shm-dmitry/pantry_signal_system/3d_models/flooding-sensor.FCStd

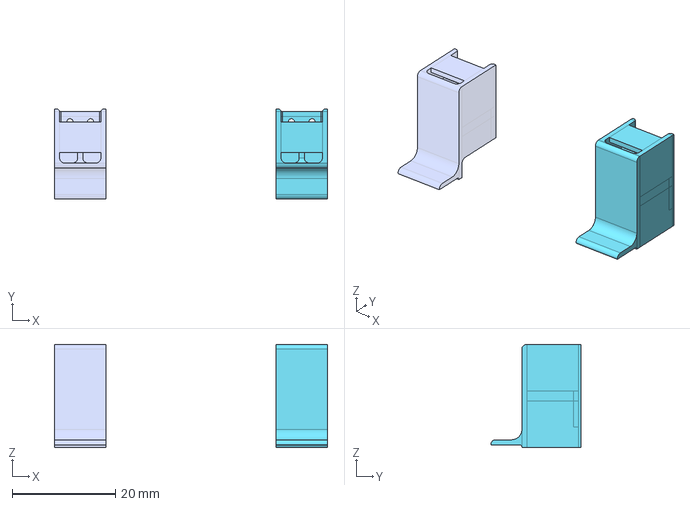
[picture p15: CAD file, 2022-12-06]
3d_models/flooding-sensor.FCStd
53.0 x 17.5 x 20.0 mm
right-side
left-side
