shm-dmitry/pantry_signal_system/3d_models/pantry_box-cup.stl

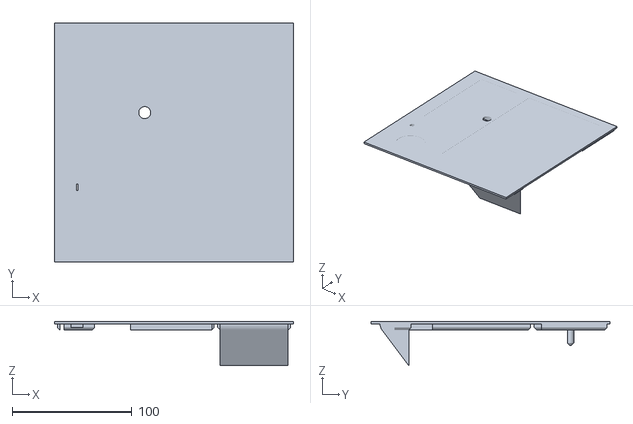
[picture p16: CAD file, 2022-12-06]
3d_models/pantry_box-cup.stl
200.0 x 200.0 x 37.0
