shm-dmitry/pantry_signal_system/3d_models/internal-flooding-sensor.FCStd

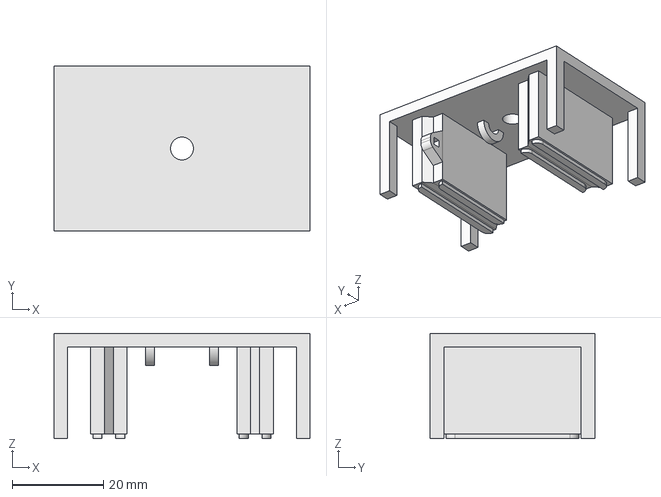
[picture p17: CAD file, 2022-07-20]
3d_models/internal-flooding-sensor.FCStd
56.0 x 36.0 x 23.0 mm
