shm-dmitry/pantry_signal_system/3d_models/supply-module-box-box.stl

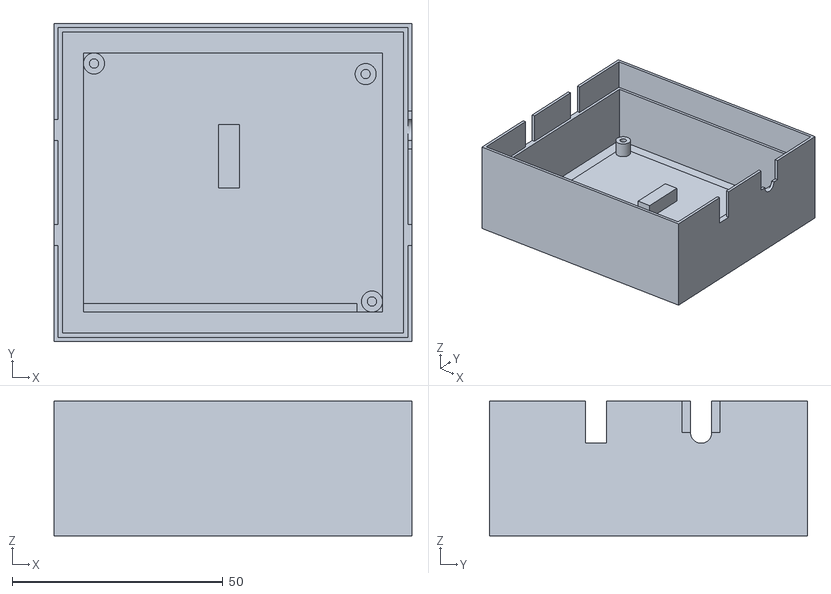
[picture p18: CAD file, 2022-04-04]
3d_models/supply-module-box-box.stl
85.0 x 75.5 x 32.0
