shm-dmitry/pantry_signal_system/3d_models/control-module-box-front.stl

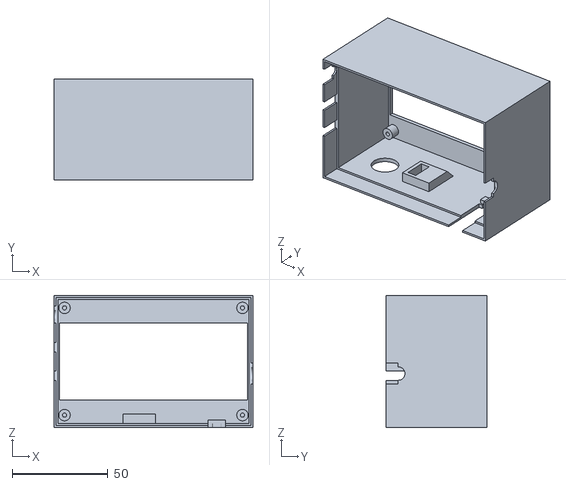
[picture p19: CAD file, 2022-04-04]
3d_models/control-module-box-front.stl
104.0 x 53.0 x 69.0
