shm-dmitry/pantry_signal_system/3d_models/23a-battery-container-box.stl

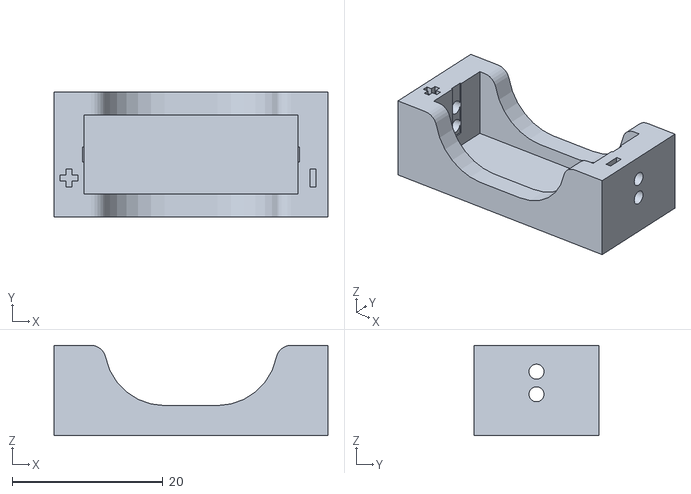
[picture p20: CAD file, 2022-04-04]
3d_models/23a-battery-container-box.stl
36.4 x 16.6 x 12.0
