shm-dmitry/pantry_signal_system/3d_models/23a-battery-container.FCStd

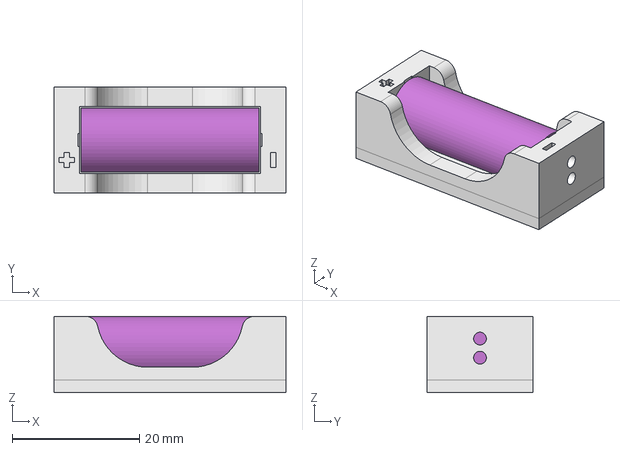
[picture p21: CAD file, 2022-04-04]
3d_models/23a-battery-container.FCStd
36.4 x 16.6 x 12.0 mm
battery-dont-print
