shm-dmitry/pantry_signal_system/3d_models/supply-module-box-cup.stl

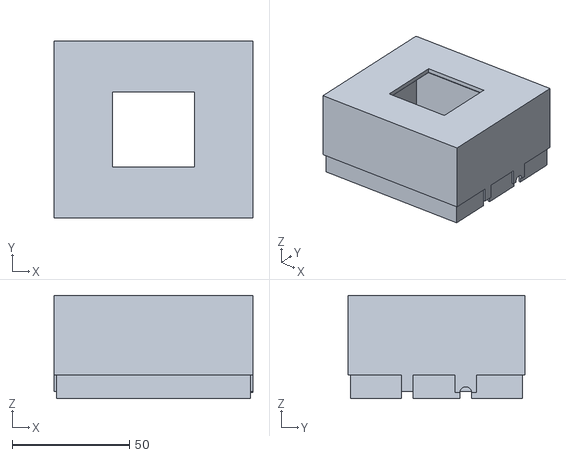
[picture p22: CAD file, 2022-04-04]
3d_models/supply-module-box-cup.stl
85.0 x 75.5 x 44.0
