shm-dmitry/pantry_signal_system/3d_models/control-module-box.FCStd

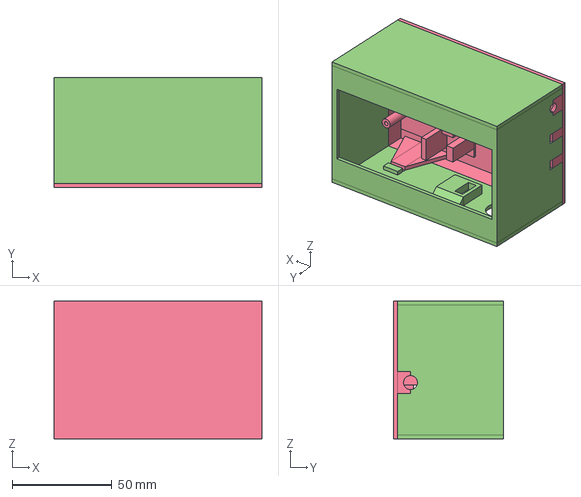
[picture p23: CAD file, 2022-04-04]
3d_models/control-module-box.FCStd
104.0 x 55.0 x 69.0 mm
front
back
