shm-dmitry/pantry_signal_system/3d_models/supply-module-box.FCStd

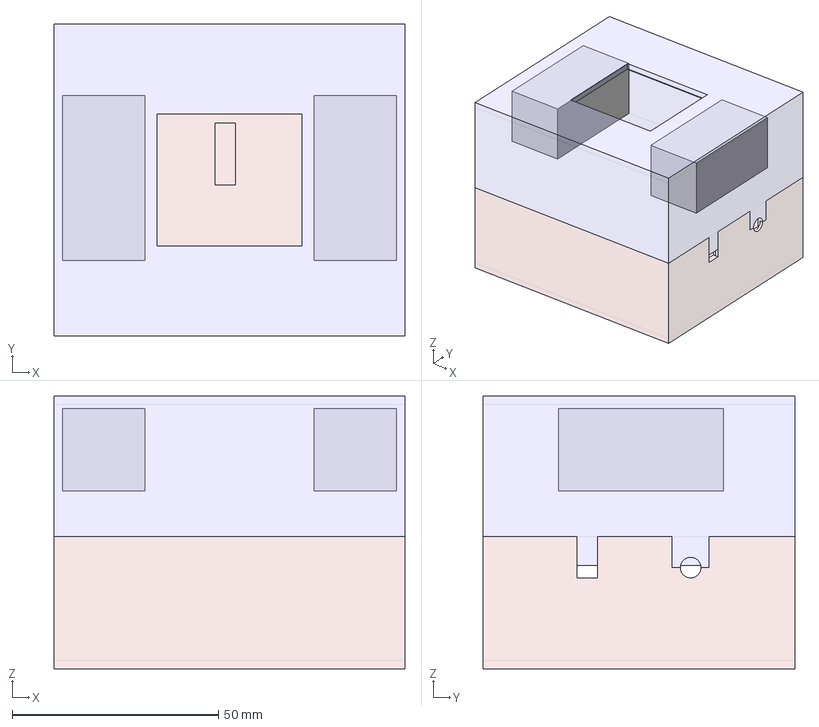
[picture p24: CAD file, 2022-04-04]
3d_models/supply-module-box.FCStd
85.0 x 75.5 x 66.0 mm
cup
alcaline-emulator-dont-print
