shm-dmitry/pantry_signal_system/3d_models/control-module-box-back.stl

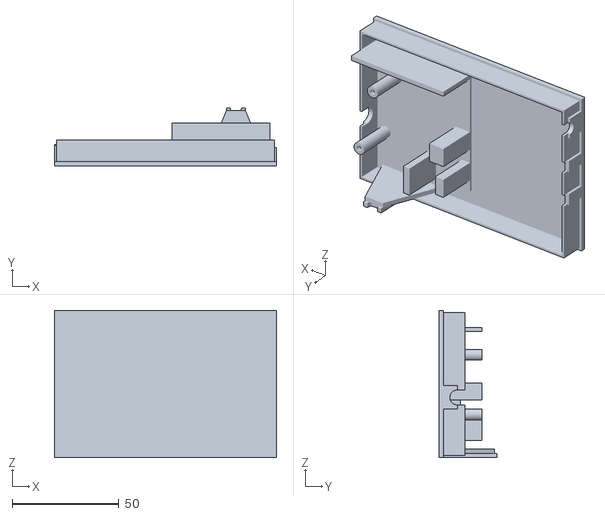
[picture p25: CAD file, 2022-03-22]
3d_models/control-module-box-back.stl
104.0 x 27.0 x 69.0
