shm-dmitry/pantry_signal_system/3d_models/air-fan-income.FCStd

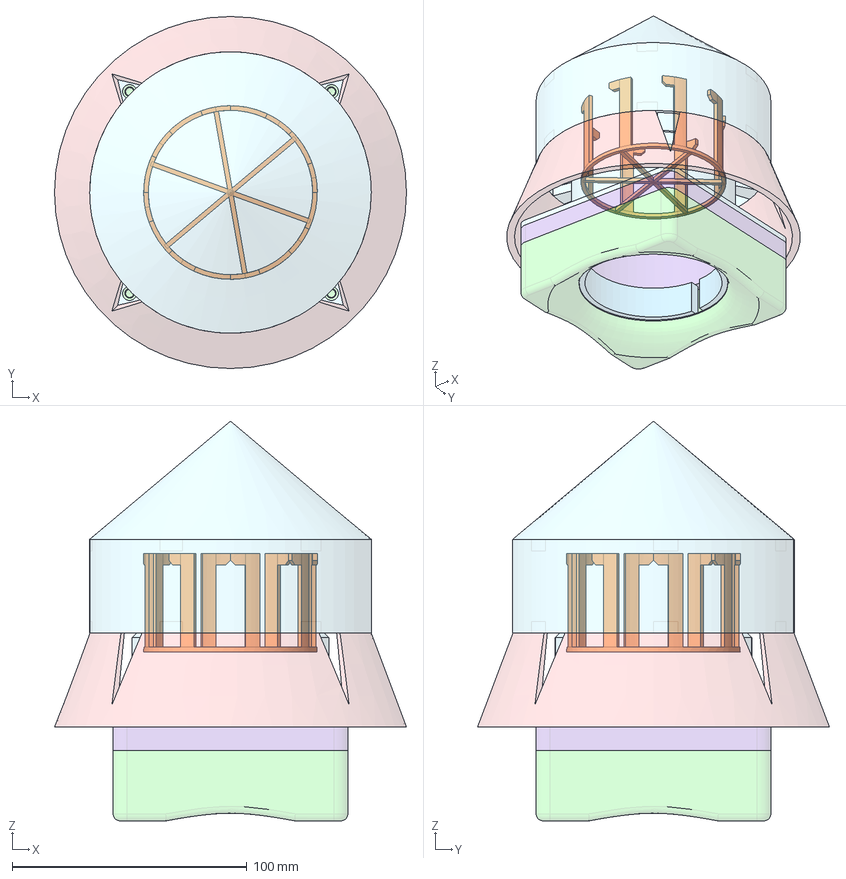
[picture p26: CAD file, 2022-03-19]
3d_models/air-fan-income.FCStd
150.0 x 150.0 x 170.3 mm
plate
top
filter
support
cap
cup-support
