shm-dmitry/pantry_signal_system/3d_models/air-fan-outcome.FCStd

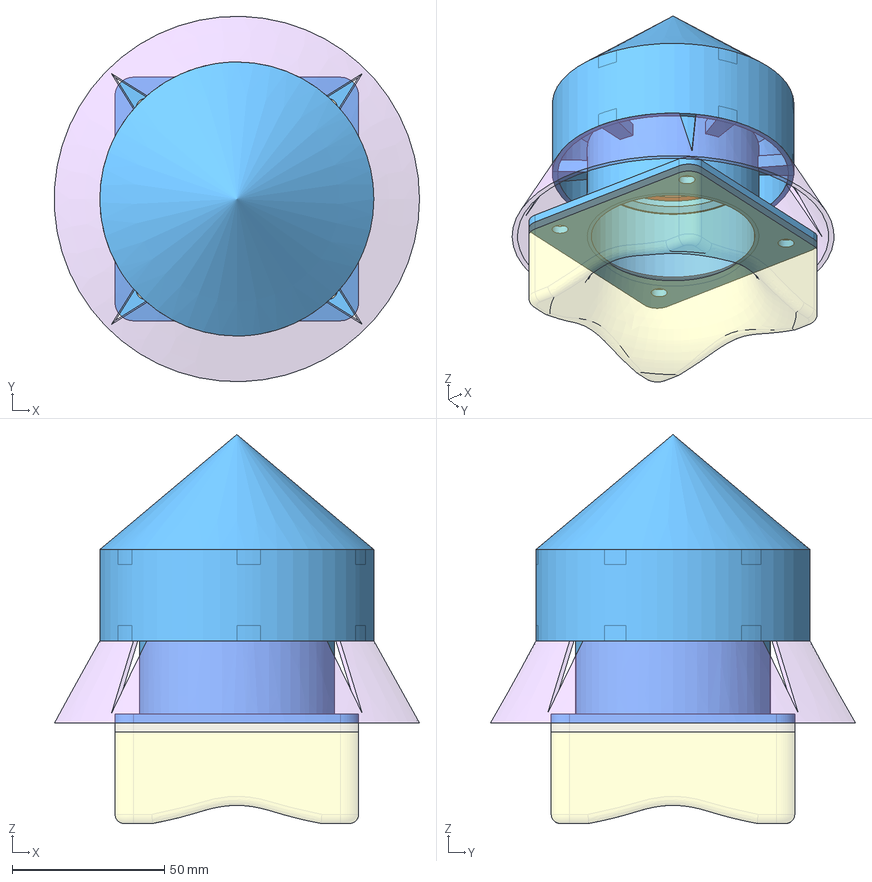
[picture p27: CAD file, 2022-03-19]
3d_models/air-fan-outcome.FCStd
119.9 x 119.9 x 127.8 mm
plate
top
filter
support
cup
