shm-dmitry/pantry_signal_system/3d_models/air-fan-box.FCStd

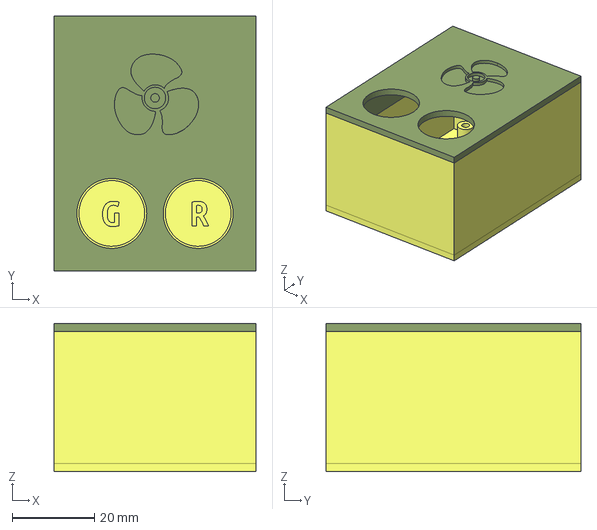
[picture p28: CAD file, 2022-03-19]
3d_models/air-fan-box.FCStd
49.0 x 62.0 x 36.0 mm
top
