shm-dmitry/pantry_signal_system/3d_models/air-fan-income-cap-support.stl

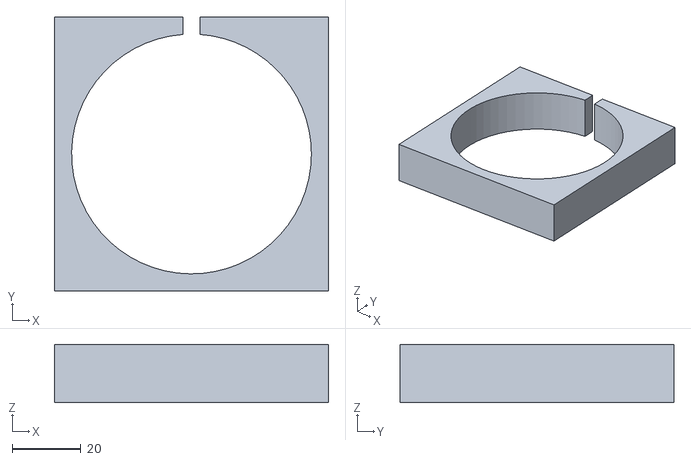
[picture p29: CAD file, 2022-03-19]
3d_models/air-fan-income-cap-support.stl
80.0 x 80.0 x 17.0
