shm-dmitry/pantry_signal_system/3d_models/air-fan-income-cap.stl

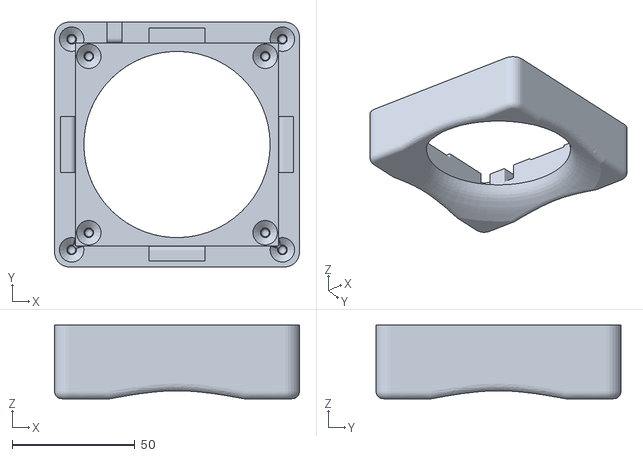
[picture p30: CAD file, 2022-03-19]
3d_models/air-fan-income-cap.stl
100.0 x 100.0 x 30.0
