shm-dmitry/pantry_signal_system/3d_models/air-fan-box-box.stl

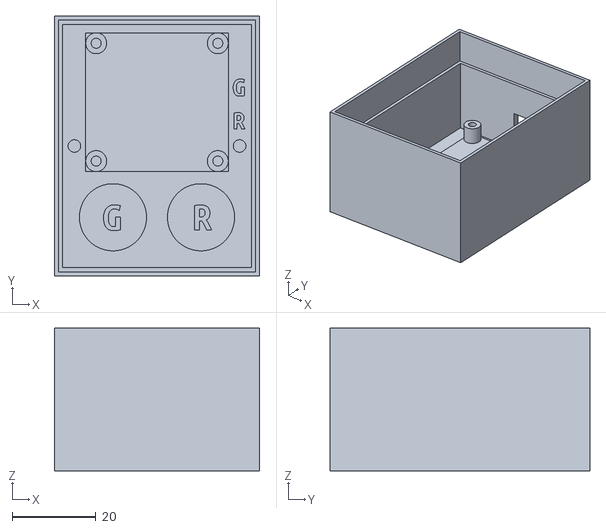
[picture p31: CAD file, 2022-03-19]
3d_models/air-fan-box-box.stl
49.0 x 62.0 x 34.0
