shm-dmitry/pantry_signal_system/3d_models/air-fan-outcome-cup.stl

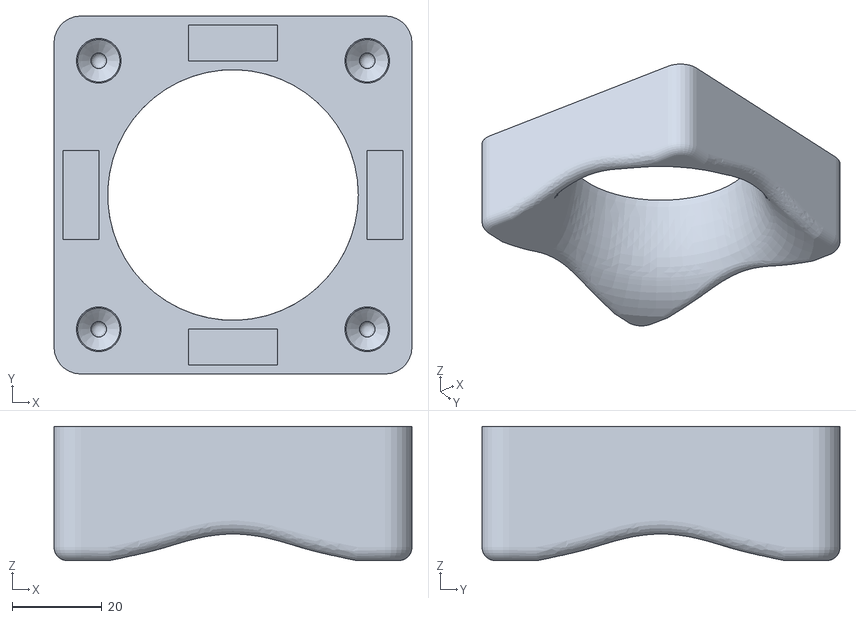
[picture p32: CAD file, 2022-03-19]
3d_models/air-fan-outcome-cup.stl
80.0 x 80.0 x 30.0
