shm-dmitry/pantry_signal_system/3d_models/air-fan-box-top.stl

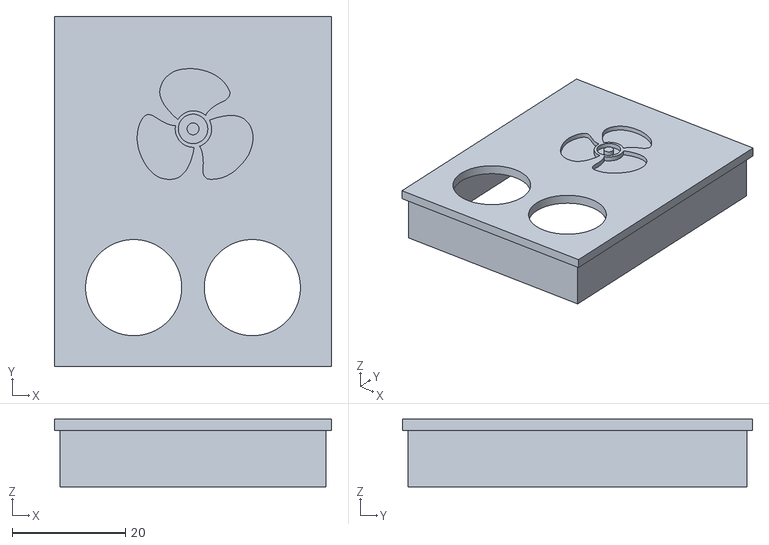
[picture p33: CAD file, 2022-03-19]
3d_models/air-fan-box-top.stl
49.0 x 62.0 x 12.0
