shm-dmitry/pantry_signal_system/3d_models/air-dryer-cup.stl

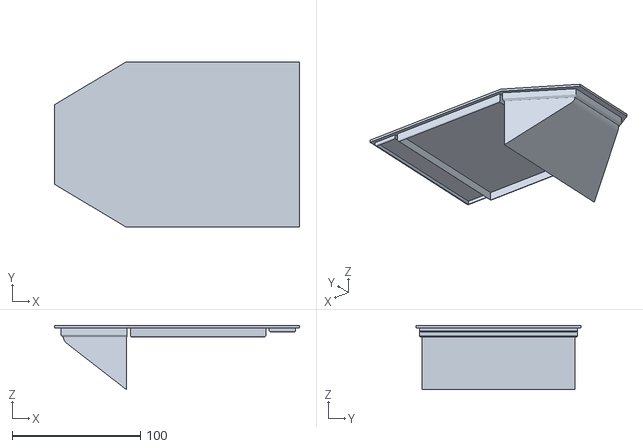
[picture p34: CAD file, 2022-03-03]
3d_models/air-dryer-cup.stl
191.0 x 129.0 x 50.0
