shm-dmitry/pantry_signal_system/3d_models/air-dryer.FCStd

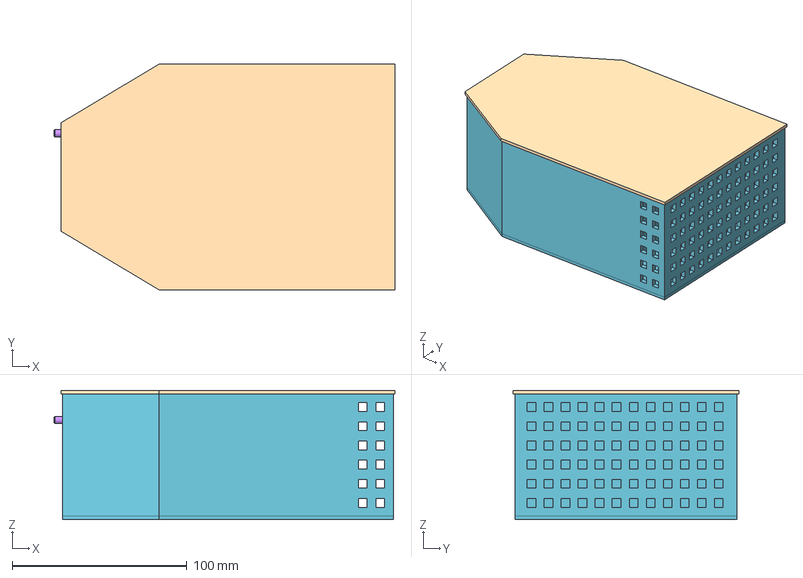
[picture p35: CAD file, 2022-03-03]
3d_models/air-dryer.FCStd
195.0 x 129.0 x 74.0 mm
container
container-cup
pin
cup
