shm-dmitry/pantry_signal_system/3d_models/air-fan-outcome-top.stl

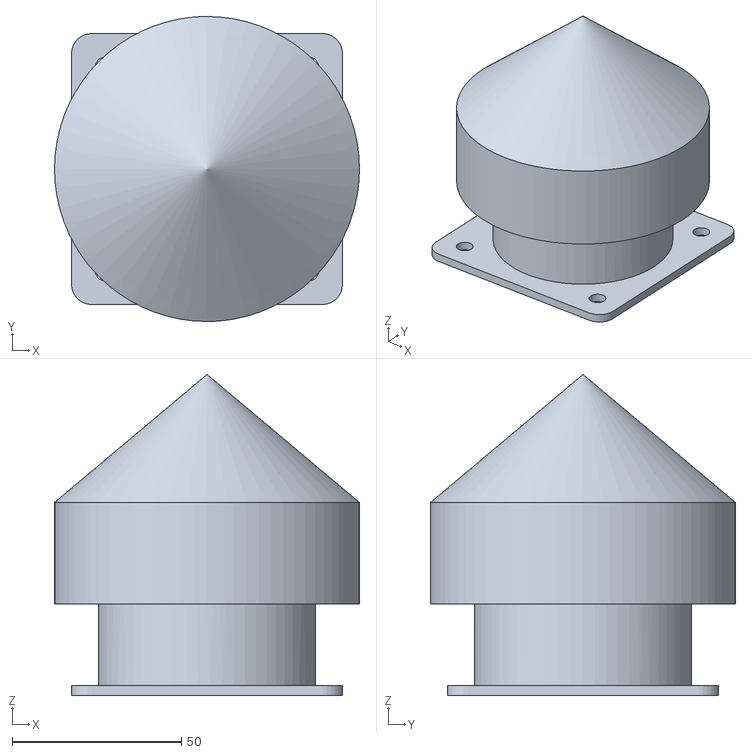
[picture p36: CAD file, 2022-03-03]
3d_models/air-fan-outcome-top.stl
90.0 x 90.0 x 94.8
