shm-dmitry/pantry_signal_system/3d_models/air-fan-income-top.stl

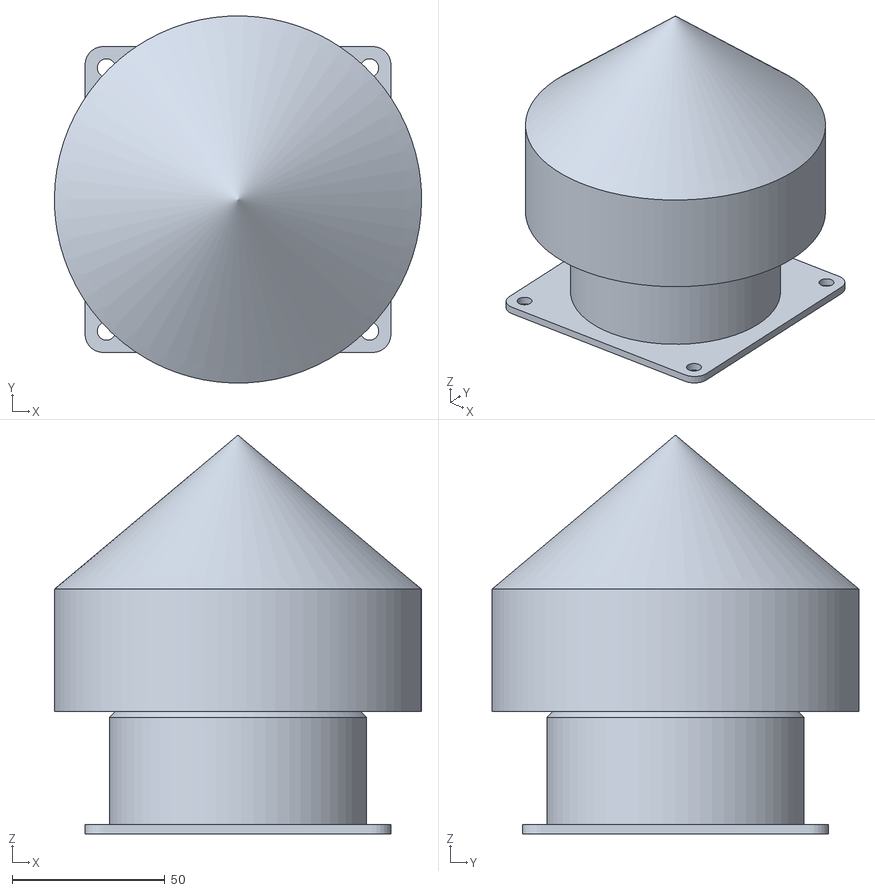
[picture p37: CAD file, 2022-03-03]
3d_models/air-fan-income-top.stl
120.0 x 119.9 x 130.3
