shm-dmitry/pantry_signal_system/3d_models/air-dryer-box.stl

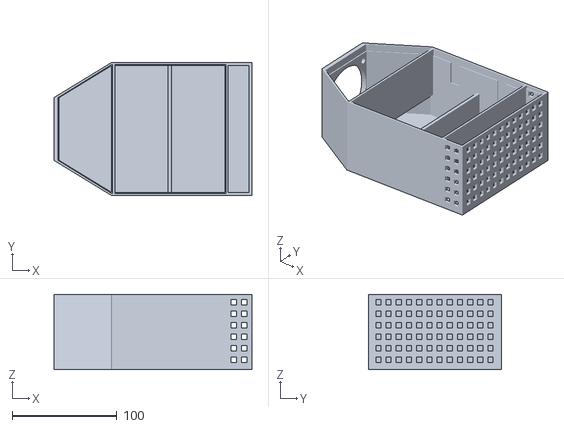
[picture p38: CAD file, 2022-03-03]
3d_models/air-dryer-box.stl
189.0 x 127.0 x 72.0
