shm-dmitry/pantry_signal_system/3d_models/air-fan-outcome-filter.stl

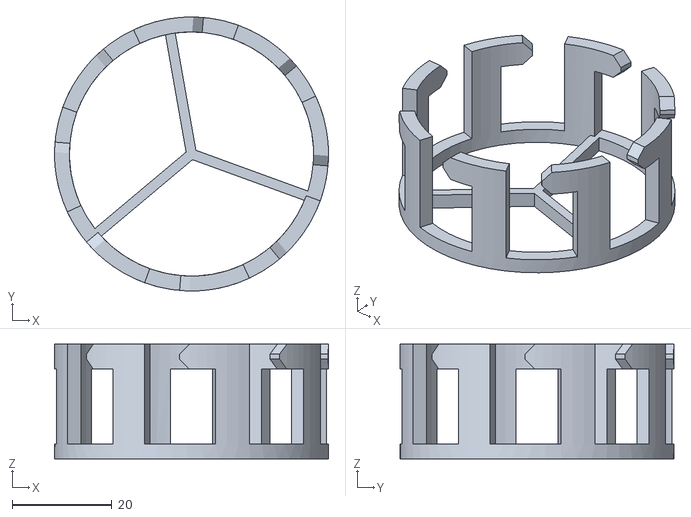
[picture p39: CAD file, 2022-03-03]
3d_models/air-fan-outcome-filter.stl
55.0 x 55.0 x 23.0
