shm-dmitry/pantry_signal_system/3d_models/air-dryer-pin.stl

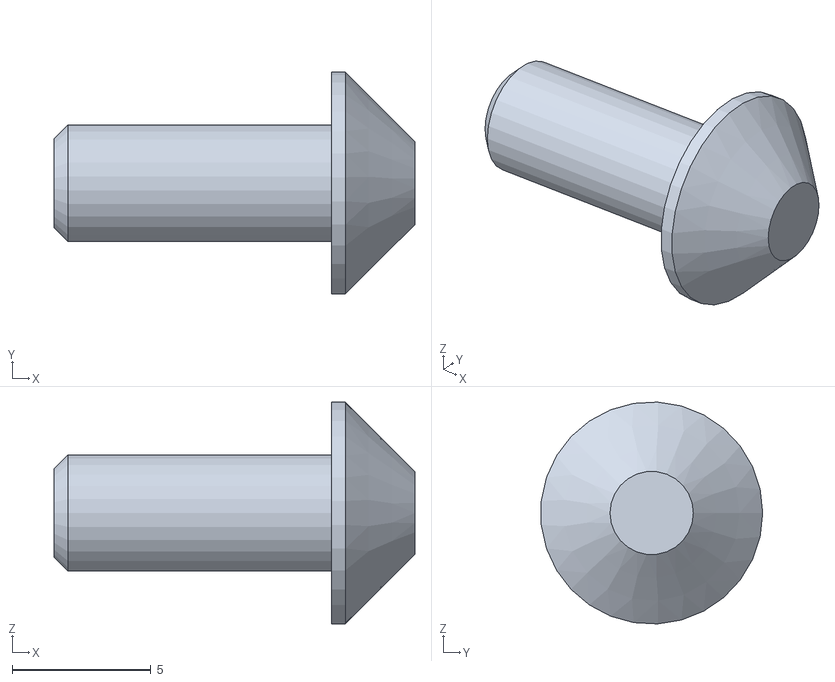
[picture p40: CAD file, 2022-03-03]
3d_models/air-dryer-pin.stl
13.0 x 7.98 x 7.99
