shm-dmitry/pantry_signal_system/3d_models/air-fan-outcome-support.stl

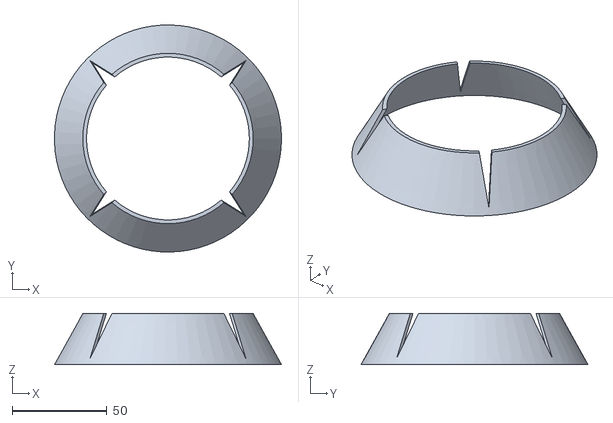
[picture p41: CAD file, 2022-02-15]
3d_models/air-fan-outcome-support.stl
120.0 x 120.0 x 27.0
