shm-dmitry/pantry_signal_system/3d_models/air-fan-outcome-plate.stl

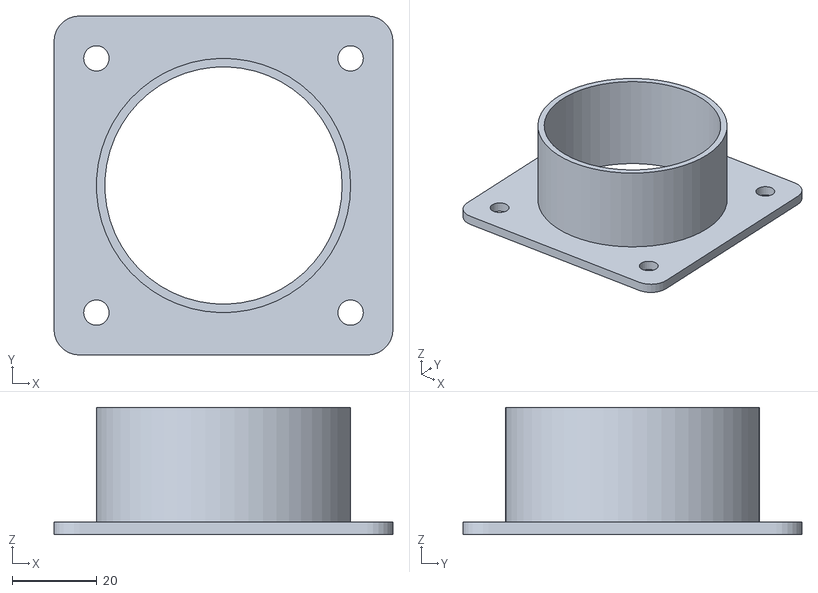
[picture p42: CAD file, 2022-02-15]
3d_models/air-fan-outcome-plate.stl
80.0 x 80.0 x 30.0
