shm-dmitry/pantry_signal_system/3d_models/air-fan-income-plate.stl

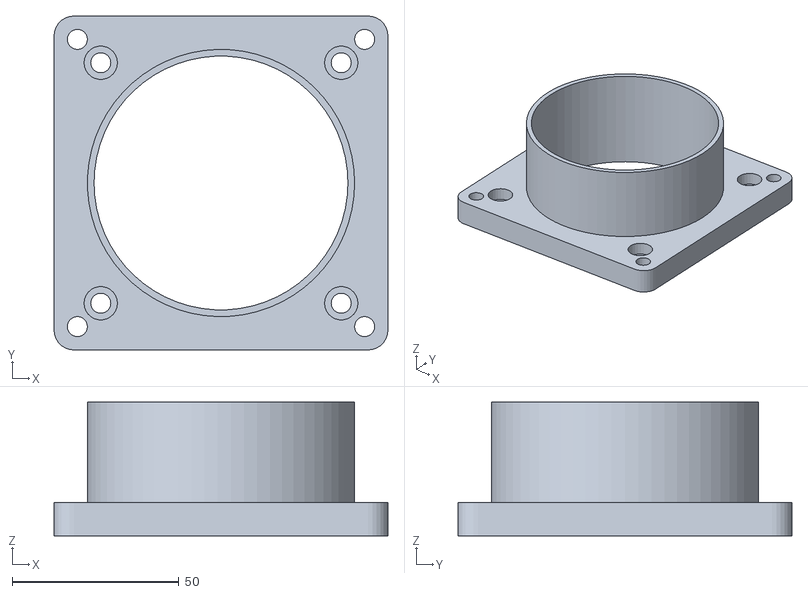
[picture p43: CAD file, 2022-02-15]
3d_models/air-fan-income-plate.stl
100.0 x 100.0 x 40.0
