shm-dmitry/pantry_signal_system/3d_models/air-fan-income-filter.stl

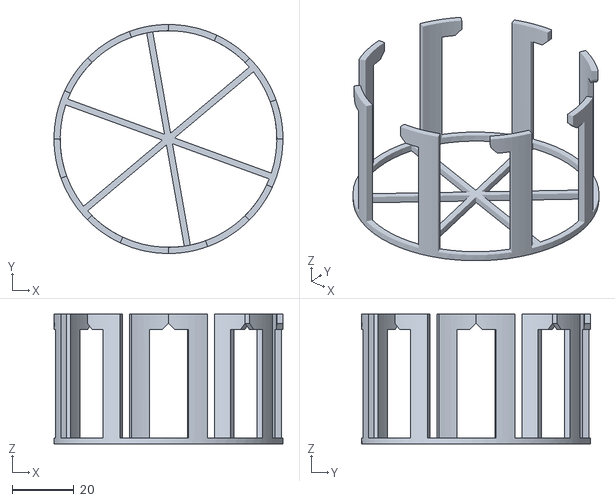
[picture p44: CAD file, 2022-02-15]
3d_models/air-fan-income-filter.stl
74.0 x 74.0 x 42.0
