shm-dmitry/pantry_signal_system/3d_models/air-fan-income-support.stl

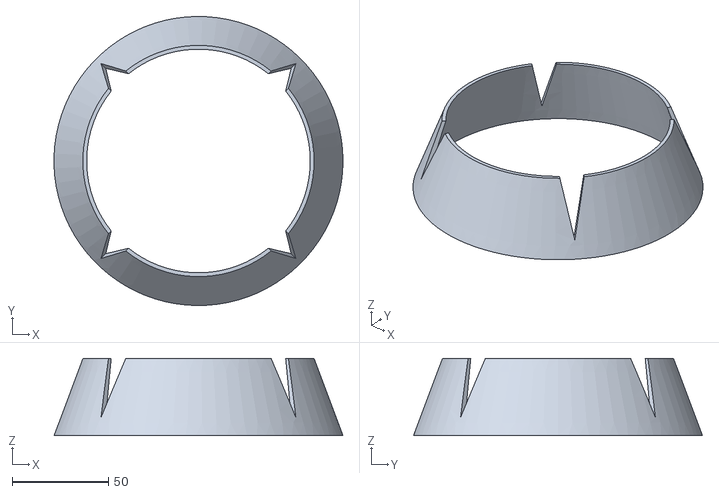
[picture p45: CAD file, 2022-02-15]
3d_models/air-fan-income-support.stl
150.0 x 150.0 x 40.0
