shm-dmitry/pantry_signal_system/3d_models/air-dryer-container.stl

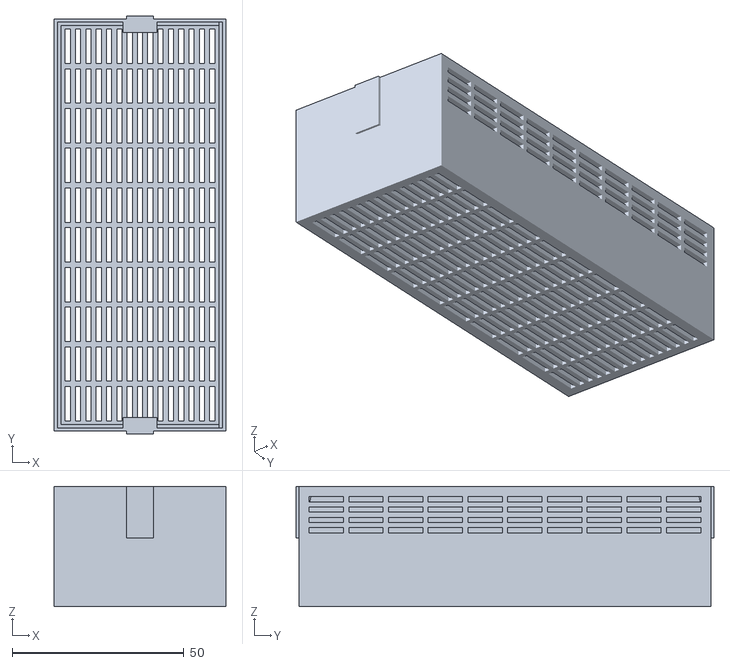
[picture p46: CAD file, 2022-02-14]
3d_models/air-dryer-container.stl
50.0 x 121.6 x 35.0
