shm-dmitry/pantry_signal_system/3d_models/air-dryer-container-cup.stl

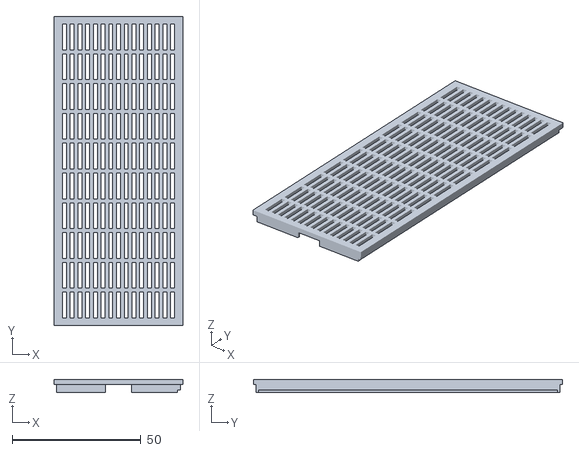
[picture p47: CAD file, 2022-02-14]
3d_models/air-dryer-container-cup.stl
50.0 x 120.0 x 5.00
