shm-dmitry/pantry_signal_system/avr/logic-module/LCD_I2C2.h

/*
    LCD_I2C - Arduino library to control a 16x2 LCD via an I2C adapter based on PCF8574
    * 2021-11-18 Brewmanz: make changes to also work for 20x4 LCD2004

    Copyright(C) 2020 Blackhack <davidaristi.0504@gmail.com>

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
    You should have received a copy of the GNU General Public License
    along with this program.If not, see < https://www.gnu.org/licenses/>.
*/

/*
 * Cloned from https://github.com/blackhack/LCD_I2C/ to change I2C interface PINS to fix problem with display
 * Problem description:
 *  I have display connected to common I2C bus. Display normal state is powerdown.
 *  In this case, when SCL and SDA pins connected to bus, display module goes I2C bus down (SCL signal has 2V)
 *  When I disconnect SDA or SCL pins from display - I2C bus starts working
 *  To fix this problem I make desigion to change PINS connected to display
 */

#ifndef _LCD_I2C2_h
#define _LCD_I2C2_h

#include "Arduino.h"
#include "SoftWire.h"

/* This struct helps us constructing the I2C output based on data and control outputs.
   Because the LCD is set to 4-bit mode, 4 bits of the I2C output are for the control outputs
   while the other 4 bits are for the 8 bits of data which are send in parts using the enable output.*/
struct OutputState
{
    uint8_t rs = 0;
    uint8_t rw = 0;
    uint8_t E = 0;
    uint8_t Led = 0;
    uint8_t data = 0;

    uint8_t GetLowData()
    {
        uint8_t buffer = rs;
        buffer |= rw << 1;
        buffer |= E << 2;
        buffer |= Led << 3;
        buffer |= (data & 0x0F) << 4;

        return buffer;
    }

    uint8_t GetHighData()
    {
        uint8_t buffer = rs;
        buffer |= rw << 1;
        buffer |= E << 2;
        buffer |= Led << 3;
        buffer |= (data & 0xF0);
        return buffer;
    }
};

class LCD_I2C2 : public Print
{
public:
    LCD_I2C2(uint8_t address, uint8_t scl, uint8_t sda, uint8_t columns, uint8_t rows)
    : _address(address), _columnMax(--columns), _rowMax(--rows), _scl(scl), _sda(sda) {}
    ~LCD_I2C2() {
      if (wire) {
        wire->end();
        delete wire;
        wire = NULL;
      }
    }

    void begin();
    void backlight();
    void noBacklight();

    void clear();
    void home();
    void leftToRight();
    void rightToLeft();
    void autoscroll();
    void noAutoscroll();
    void display();
    void noDisplay();
    void cursor();
    void noCursor();
    void blink();
    void noBlink();
    void scrollDisplayLeft();
    void scrollDisplayRight();
    void createChar(uint8_t location, uint8_t charmap[]);
    void setCursor(uint8_t col, uint8_t row);

    // Method used by the Arduino class "Print" which is the one that provides the .print(string) method
    virtual size_t write(uint8_t character);

private:
    void InitializeLCD();
    void I2C_Write(uint8_t output);
    void LCD_Write(uint8_t output, bool initialization = false);

private:
    uint8_t _address;
    uint8_t _columnMax;
    uint8_t _rowMax;
    OutputState _output;
    uint8_t _displayState = 0x00;
    uint8_t _entryState = 0x00;
    uint8_t _scl = 0xFF;
    uint8_t _sda = 0xFF;
    SoftWire * wire = NULL;
    char txbuffer[4];
};

#endif
