shm-dmitry/pantry_signal_system/avr/logic-module/display.ino

#include <Wire.h> 
#include "LCD_I2C2.h"

#define ENABLE_DISPLAY_PIN  A3
#define DISPLAY_PIN_SDA     12
#define DISPLAY_PIN_SCL     13
#define DISPLAY_ROW_COUNT   4
#define DISPLAY_COL_COUNT   20
#define DISPLAY_I2C_ADDRESS 0x27

#define DISPLAY_PRINT_BATTERY_LEVEL(index, v, pc, is_active) { \
  lcd.setCursor(0, index - 1); \
  lcd.print("B"); \
  lcd.print(index); \
  if (is_active) { \
    lcd.print("> "); \
  } else { \
    lcd.print("  "); \
  } \
  if (v < 100) { \
    lcd.print(" "); \
  } \
  lcd.print(v / 10.0, 1); \
  lcd.print("V "); \
  lcd.print(pc); \
  lcd.print("% "); \
  if (pc < 10) { \
    lcd.print("  "); \
  } else if (pc < 100) { \
    lcd.print(" "); \
  } \
  if (((uint16_t)pc * 5 / 100) == 0) { \
    lcd.print("X"); \
  } else { \
    for (uint8_t i = 0; i<((uint16_t)pc * 5 / 100) && i < 5; i++) { \
      lcd.print("\xFF"); \
    } \
  }\
} 

#define DISPLAY_PRINT_T(t) { \
  lcd.setCursor(0, 3); \
  lcd.print("T "); \
  if (t < 100) { \
    lcd.print(" "); \
  } \
  lcd.print(t / 10.0, 1); \
  lcd.print("c"); \
}

#define DISPLAY_PRINT_HUM(h) { \
  lcd.setCursor(8, 3); \
  lcd.print("H "); \
  if (h < 100) { \
    lcd.print(" "); \
  } \
  lcd.print(h / 10.0, 1); \
  lcd.print("%"); \
}

#define DISPLAY_PRINT_ALARM(is_indoor_flooding, is_outdoor_flooding) { \
  lcd.setCursor(16, 3); \
  if (is_indoor_flooding && is_outdoor_flooding) { \
    lcd.print("ALRM"); \
  } else if (is_indoor_flooding) { \
    lcd.print("W-IN"); \
  } else if (is_outdoor_flooding) { \
    lcd.print("W-EX"); \
  } else { \
    lcd.print(" OK "); \
  } \
}

void display_init() {
  pinMode(ENABLE_DISPLAY_PIN, OUTPUT);
  digitalWrite(ENABLE_DISPLAY_PIN, LOW);
  Serial.println("Display OK");
}

void display_off() {
  Serial.println("Display OFF");

  digitalWrite(ENABLE_DISPLAY_PIN, LOW);
}

void display_write(const ModuleData * data) {
  digitalWrite(ENABLE_DISPLAY_PIN, HIGH);
  delay(50); // await display startup

  Serial.println("Display ON");

  LCD_I2C2 lcd(DISPLAY_I2C_ADDRESS, DISPLAY_PIN_SCL, DISPLAY_PIN_SDA, DISPLAY_COL_COUNT, DISPLAY_ROW_COUNT); 
  lcd.begin();
  lcd.backlight();

  DISPLAY_PRINT_BATTERY_LEVEL(1, data->battery1_voltage_x10, data->battery1_percent, data->active_battery == 1);
  DISPLAY_PRINT_BATTERY_LEVEL(2, data->battery2_voltage_x10, data->battery2_percent, data->active_battery == 2);
  DISPLAY_PRINT_BATTERY_LEVEL(3, data->battery3_voltage_x10, data->battery3_percent, data->active_battery == 3);

  DISPLAY_PRINT_T(data->temperature_x10);
  DISPLAY_PRINT_HUM(data->humidity_x10);

  DISPLAY_PRINT_ALARM(data->indoor_flooding_sensor_alarm, data->outdoor_flooding_sensor_alarm);
}

void display_write_message(const char * message) {
  digitalWrite(ENABLE_DISPLAY_PIN, HIGH);
  delay(50); // await display startup

  Serial.println("Display ON");

  LCD_I2C2 lcd(DISPLAY_I2C_ADDRESS, DISPLAY_PIN_SCL, DISPLAY_PIN_SDA, DISPLAY_COL_COUNT, DISPLAY_ROW_COUNT); 
  lcd.begin();
  lcd.backlight();
  lcd.clear();

  lcd.print(message);
}
