shm-dmitry/pantry_signal_system/esp32/lora_receiver/main/log.h

#ifndef MAIN_LOG_H_
#define MAIN_LOG_H_

#include "esp_log.h"

#define WIFI_LOG "wifi_log"
#define MQTT_LOG "mqtt_log"
#define NVS_LOG "nvs_log"
#define SNMP_LOG "snmp_log"
#define LORA_LOG "lora_log"
#define JSON_LOG "json_log"

#endif /* MAIN_LOG_H_ */
