shm-dmitry/pantry_signal_system/avr/logic-module/encrypter.ino

#include "encrypter_secret.h"

uint8_t encrypter_send_key_offset = 0;
uint8_t encrypter_byte_1 = 0;
uint8_t encrypter_byte_2 = 0;
uint16_t encrypter_crc = 0;

uint8_t encrypter_init() {
  randomSeed(analogRead(0));
  encrypter_reset();
  Serial.println("Encrypter OK");
}

uint8_t encrypter_reset() {
  encrypter_send_key_offset = 0;
  encrypter_byte_1 = 0;
  encrypter_byte_2 = 0;
  encrypter_crc = 0;
}

uint8_t encrypter_next_random() {
  return random(256);
}

uint8_t encrypt_next(uint8_t value) {
  encrypter_crc += value;
  
  uint8_t secret[ENCRYPTER_SEND_SECRET_KEY_SIZE] = ENCRYPTER_SEND_SECRET_KEY;

  if (encrypter_send_key_offset >= secret) {
    encrypter_send_key_offset = 0;
  }

  uint8_t result = value ^ encrypter_byte_1 ^ encrypter_byte_2 ^ secret[encrypter_send_key_offset++];
  encrypter_byte_1 = encrypter_byte_2;
  encrypter_byte_2 = value;
  return result;
}

uint16_t encrypter_get_crc() {
  return encrypter_crc;
}
