shm-dmitry/pantry_signal_system/avr/logic-module/flooding.ino

#define INDOOR_PIN A0
#define OUTDOOR_PIN A1

#define FLOOING_ALARM_VALUE 300

void flooding_init() {
  pinMode(INDOOR_PIN,  INPUT);
  pinMode(OUTDOOR_PIN,  INPUT);
  Serial.println("Flooding sensors OK");
}

boolean flooding_indoor_check_ok() {
  int val = analogRead(INDOOR_PIN);
  return val > FLOOING_ALARM_VALUE;
}

boolean flooding_outdoor_check_ok() {
  int val = analogRead(OUTDOOR_PIN);
  return val > FLOOING_ALARM_VALUE;
}
