shm-dmitry/pantry_signal_system/esp32/lora_receiver/main/lora/lora_decrypter.c

#include "lora_decrypter.h"
#include "../../../../avr/logic-module/encrypter_secret.h"

uint8_t decrypter_send_key_offset = 0;
uint8_t decrypter_byte_1 = 0;
uint8_t decrypter_byte_2 = 0;
uint16_t decrypter_crc = 0;

const uint8_t LORA_ENCRYPTER_SECRET_KEY[ENCRYPTER_SEND_SECRET_KEY_SIZE] = ENCRYPTER_SEND_SECRET_KEY;

void decrypter_reset() {
	decrypter_send_key_offset = 0;
	decrypter_byte_1 = 0;
	decrypter_byte_2 = 0;
	decrypter_crc = 0;
}

uint8_t decrypter_decrypt_byte(uint8_t value) {
	if (decrypter_send_key_offset >= ENCRYPTER_SEND_SECRET_KEY_SIZE) {
		decrypter_send_key_offset = 0;
	}

	value = value ^ decrypter_byte_1 ^ decrypter_byte_2 ^ LORA_ENCRYPTER_SECRET_KEY[decrypter_send_key_offset++];
	decrypter_byte_1 = decrypter_byte_2;
	decrypter_byte_2 = value;

	decrypter_crc += value;

	return value;
}

uint16_t decrypter_get_crc() {
	return decrypter_crc;
}
